HummingbirdHammocks/ultralight-hammocks/Double/Graphics/Backgrounds/DoubleHammockBackground.jpg

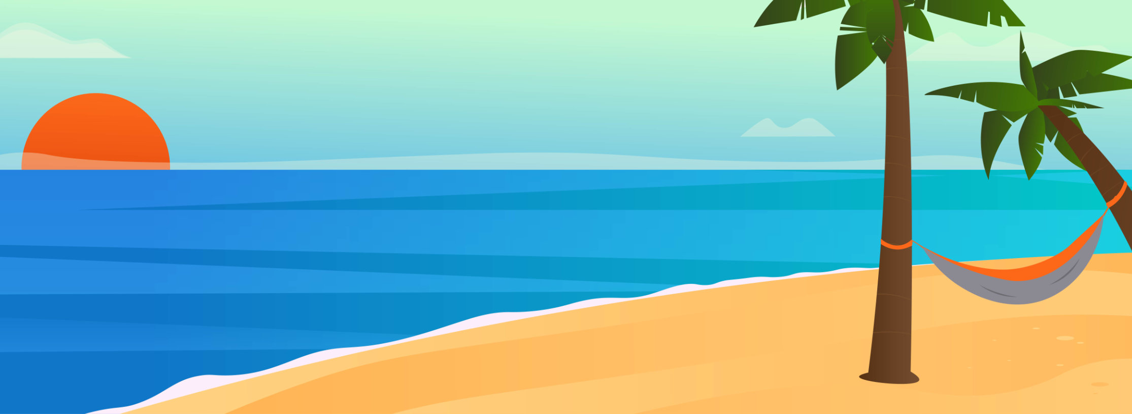
Double/Graphics/Backgrounds/DoubleHammockBackground.jpg
