HummingbirdHammocks/ultralight-hammocks/Double/Graphics/Backgrounds/Landscape_4 Double Hammock_2704x1520-02.jpg

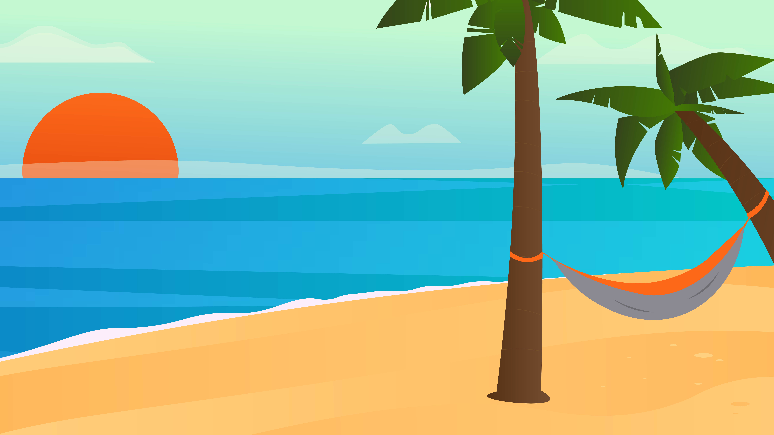
Double/Graphics/Backgrounds/Landscape_4 Double Hammock_2704x1520-02.jpg
