HummingbirdHammocks/ultralight-hammocks/Long/Graphics/Backgrounds/Landscape_3 Long Hammock_2704x1520-02.jpg

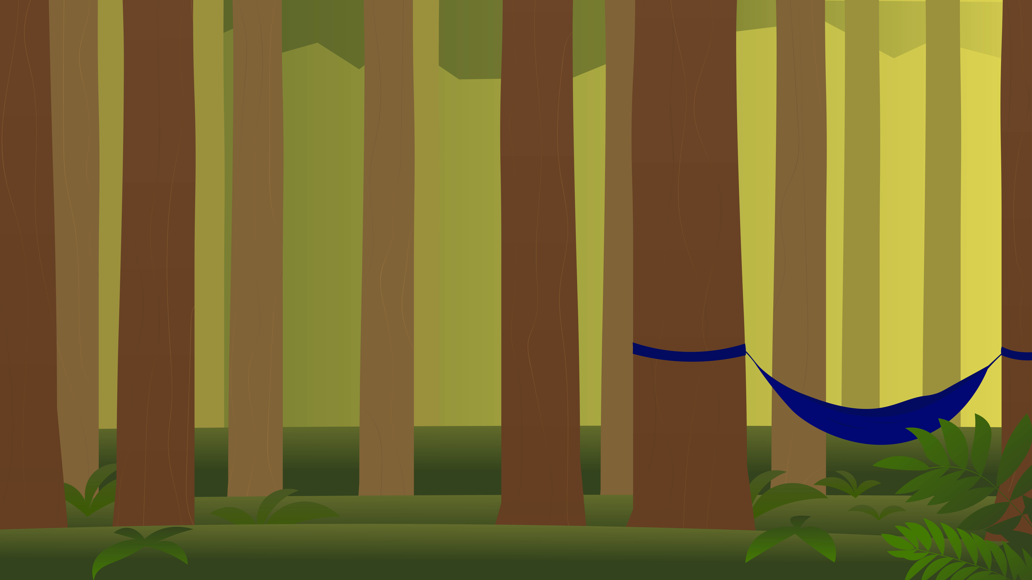
Long/Graphics/Backgrounds/Landscape_3 Long Hammock_2704x1520-02.jpg
