HummingbirdHammocks/ultralight-hammocks/Single/Graphics/Background/Landscape_2.jpg

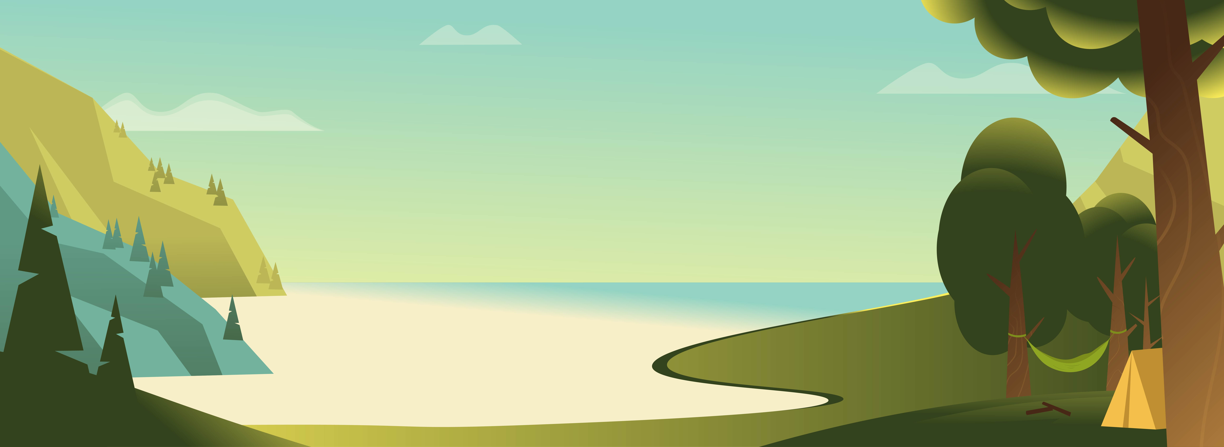
Single/Graphics/Background/Landscape_2.jpg
