HummingbirdHammocks/ultralight-hammocks/Single/Graphics/Background/Landscape_3.jpg

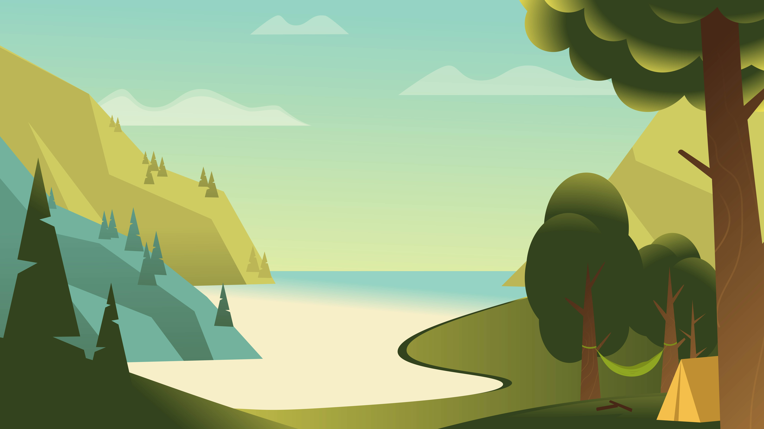
Single/Graphics/Background/Landscape_3.jpg
