HummingbirdHammocks/ultralight-hammocks/Single/Graphics/Model/Hammocks_1.1247.jpg

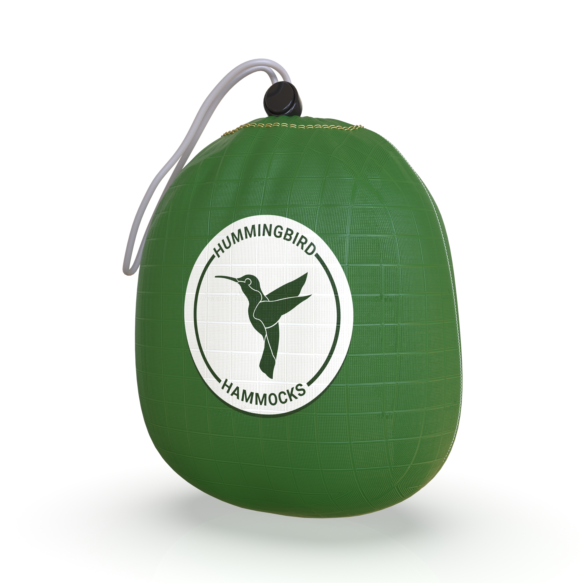
Single/Graphics/Model/Hammocks_1.1247.jpg
