HummingbirdHammocks/ultralight-hammocks/SinglePlus/Graphics/Backgrounds/Landscape_2 Single_ Hammock_2 Single_ Hammock  2230X815.jpg

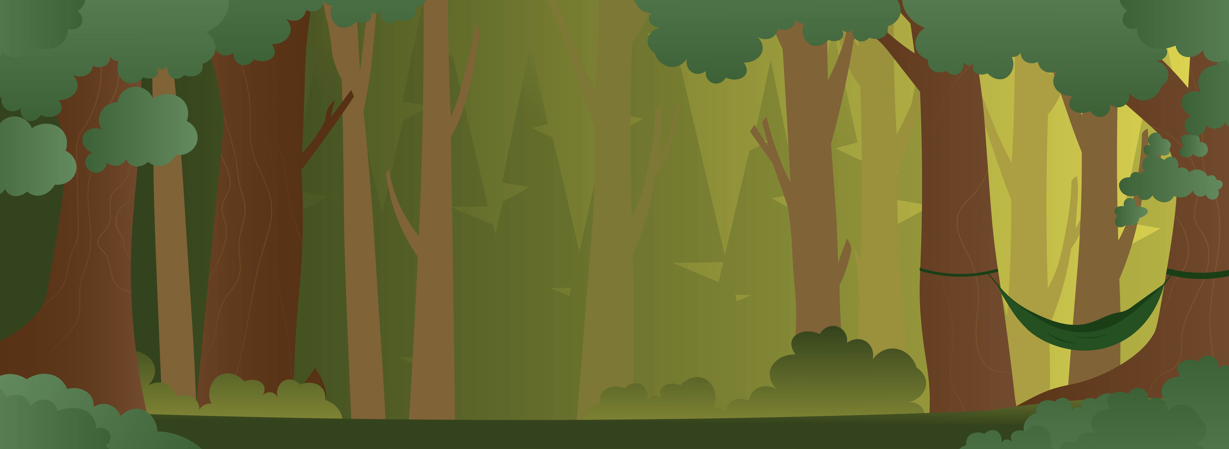
SinglePlus/Graphics/Backgrounds/Landscape_2 Single_ Hammock_2 Single_ Hammock 2230X815.jpg
